TinyCircuits/TinyCircuits-Wireling-IR-Emitter-AST1026/cad/Wireling_IR_EMITTER_AST1026_REV2-DETAILED_DRAWING-PNG.png

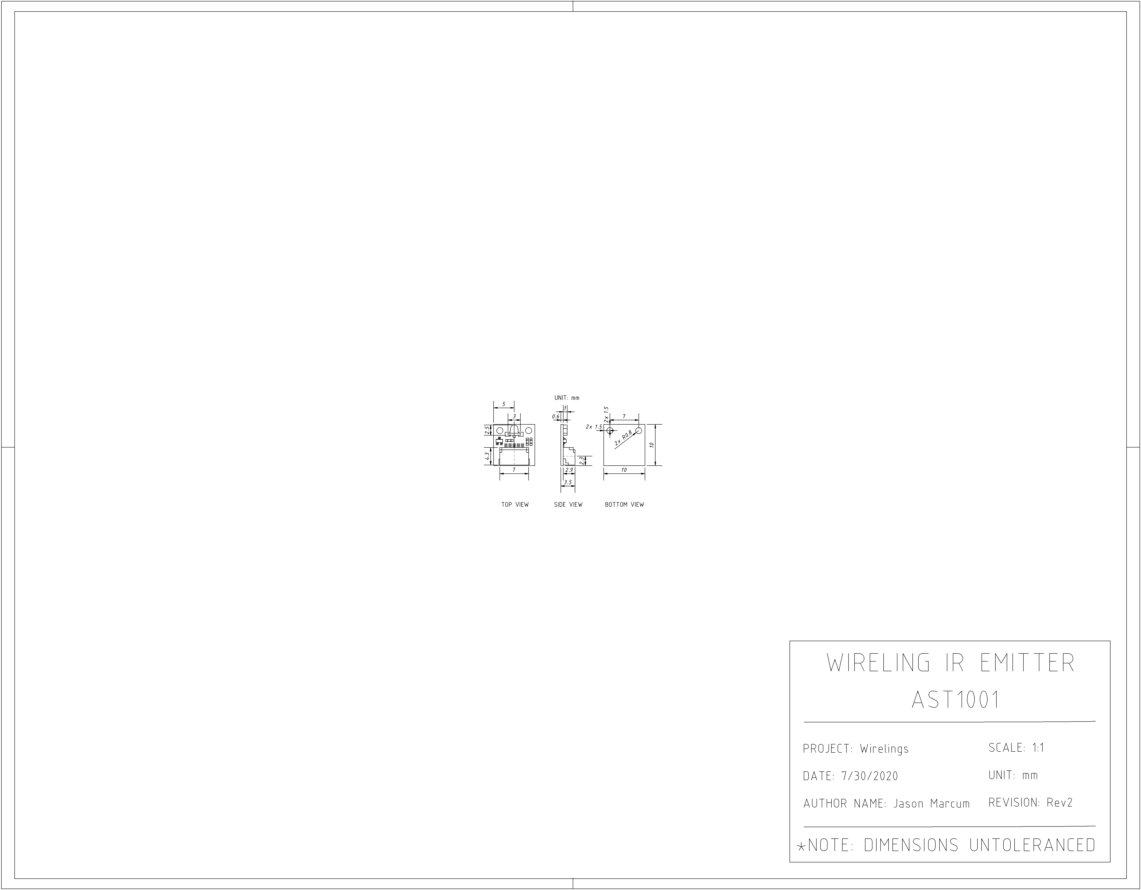
cad/Wireling_IR_EMITTER_AST1026_REV2-DETAILED_DRAWING-PNG.png
